AbdullahHendy/Speaker-PCB/Simulation/DC reg sim.asc

C1: cap; 10µ; Rser=0.1
C2: cap; 10µ
C3: cap; 0.1µ
C4: cap; 100µ; Rser=0.1
D1: diode; 1N4148
D2: diode; 1N4148
L1: ind; 4µ
R1: res; 3.57k
R2: res; 240
U1: LT317A
V1: voltage; 24
V2: voltage; SINE(0 0.1 10k); AC 0.1
Named nets: 0
;tran 1m
.ac dec 100 1 100k
